SimonMerrett/SOICbite/adaptors/SOICbite_USB/images/rev2_3D_front.png

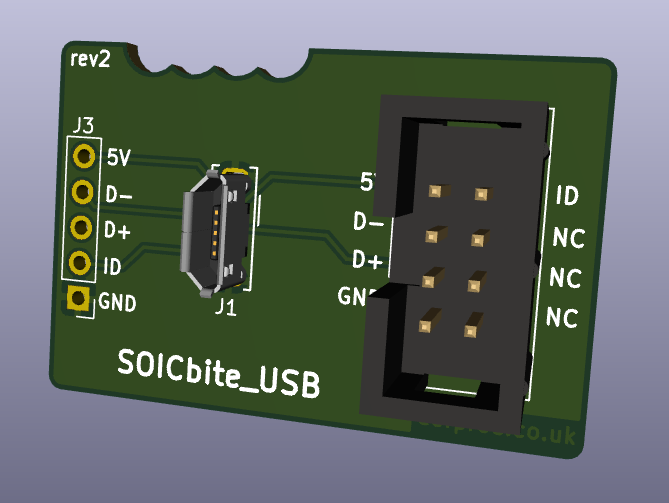
adaptors/SOICbite_USB/images/rev2_3D_front.png
