SimonMerrett/SOICbite/gEDA/images/top.png

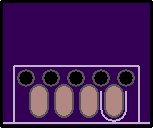
gEDA/images/top.png
