SimonMerrett/SOICbite/images/Eagle Library.PNG

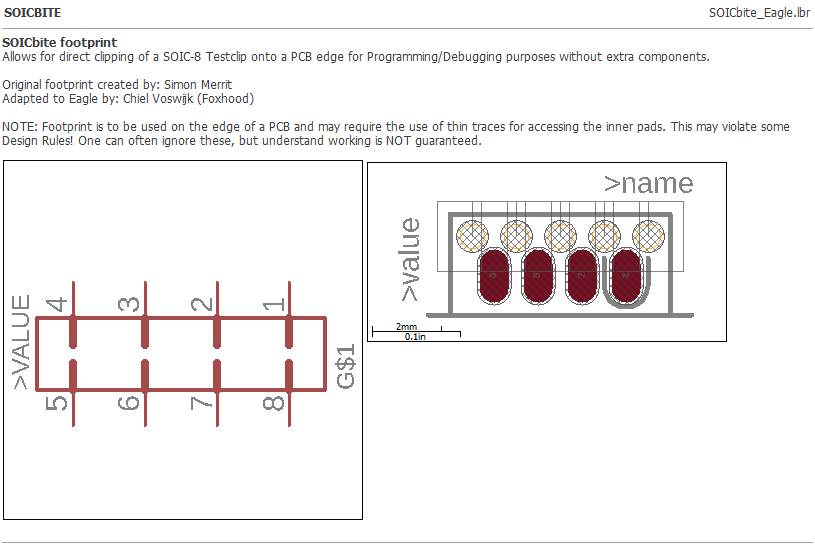
images/Eagle Library.PNG
