SimonMerrett/SOICbite/images/KiCAD_Footprint.png

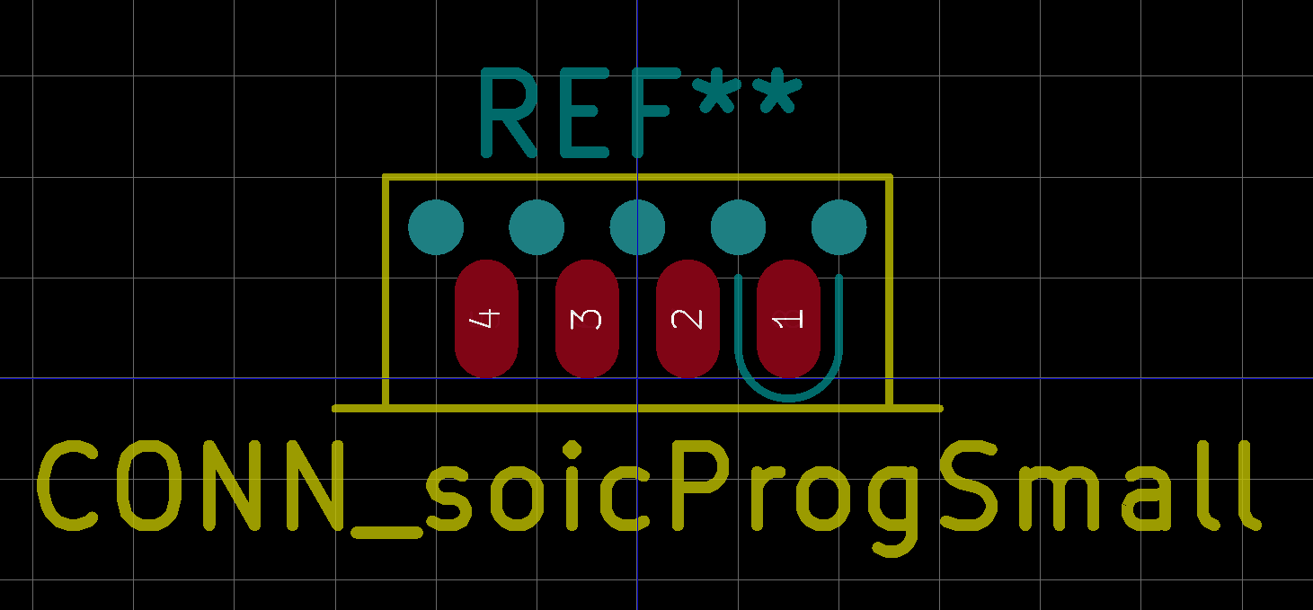
images/KiCAD_Footprint.png
