SimonMerrett/SOICbite/images/slot_cutout_clip_side.jpeg

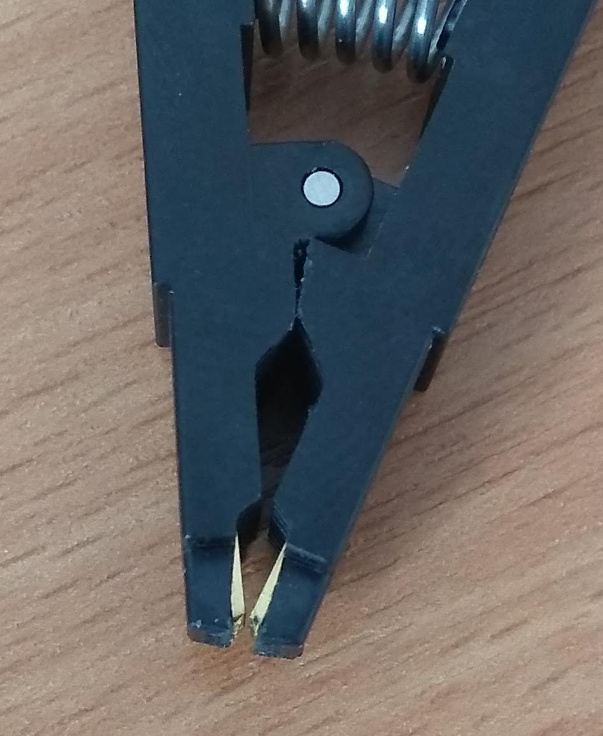
images/slot_cutout_clip_side.jpeg
