SimonMerrett/SOICbite/images/Unchecked Dimensional Drawing.PNG

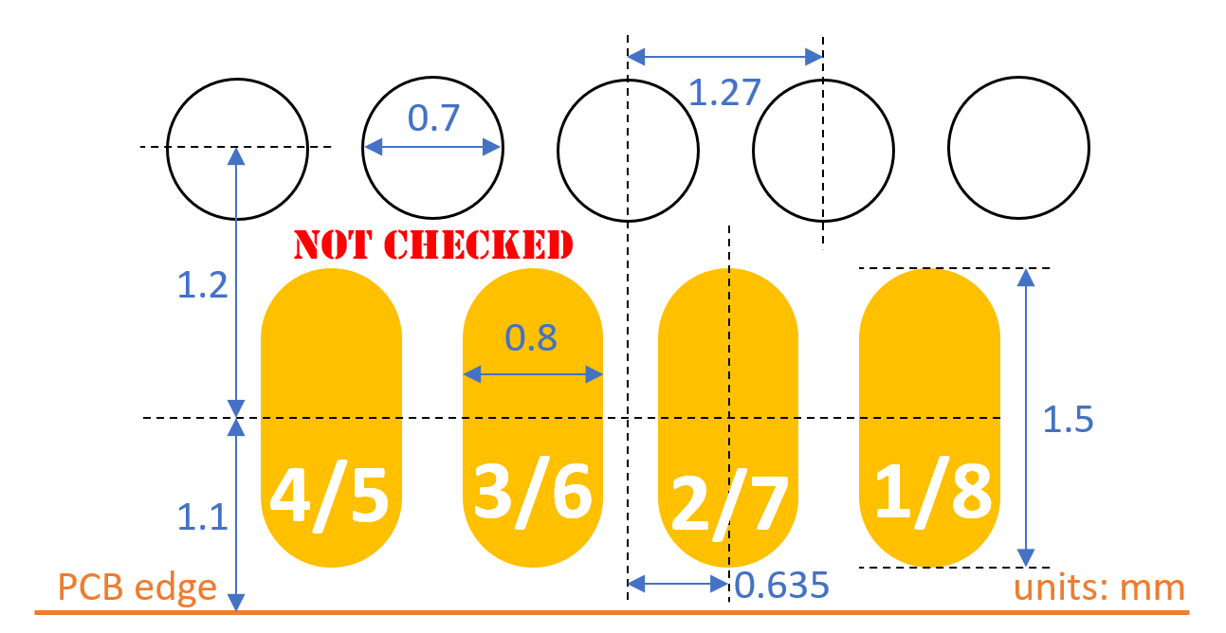
images/Unchecked Dimensional Drawing.PNG
